CeSiumUA/homepost/main/ble_scanner.c

#include "ble_scanner.h"

static const char *TAG = __FILE__;

ble_scanned_device_cb_t ble_scanned_device_cb;

static esp_ble_scan_params_t ble_scan_params = {
    .scan_type              = BLE_SCAN_TYPE_PASSIVE,
    .own_addr_type          = BLE_ADDR_TYPE_PUBLIC,
    .scan_filter_policy     = BLE_SCAN_FILTER_ALLOW_ALL,
    .scan_interval          = 0x50,
    .scan_window            = 0x30,
    .scan_duplicate         = BLE_SCAN_DUPLICATE_DISABLE
};

#ifdef CONFIG_HOMEPOST_PRINT_BLE_DEVICE_NAME
static void ble_scanner_get_device_name(esp_ble_gap_cb_param_t *param, char *name, int name_len){
    uint8_t *adv_name = NULL;
    uint8_t adv_name_len = 0;

    adv_name = esp_ble_resolve_adv_data(param->scan_rst.ble_adv, ESP_BLE_AD_TYPE_NAME_CMPL, &adv_name_len);

    if (adv_name != NULL && adv_name_len > 0) {
        snprintf(name, name_len, "%.*s", adv_name_len, adv_name);
    }
    else {
        snprintf(name, name_len, "Unknown device");
    }
}
#endif

static void ble_scanner_gap_cb(esp_gap_ble_cb_event_t event, esp_ble_gap_cb_param_t *param){
#ifdef CONFIG_HOMEPOST_PRINT_BLE_DEVICE_NAME
    char name[64];
#endif
    esp_err_t err;

    switch (event) {
        case ESP_GAP_BLE_SCAN_PARAM_SET_COMPLETE_EVT:
            ESP_LOGI(TAG, "ESP_GAP_BLE_SCAN_PARAM_SET_COMPLETE_EVT");
            if (param->scan_param_cmpl.status == ESP_BT_STATUS_SUCCESS) {
                ESP_LOGI(TAG, "Scan parameters set successfully");
                esp_ble_gap_start_scanning(0);
            }
            else {
                ESP_LOGE(TAG, "Unable to set scan parameters");
            }
            break;
        case ESP_GAP_BLE_SCAN_START_COMPLETE_EVT:
            if ((err = param->scan_start_cmpl.status) != ESP_BT_STATUS_SUCCESS) {
                ESP_LOGE(TAG, "Scan start failed: %s", esp_err_to_name(err));
            }
            break;
        case ESP_GAP_BLE_ADV_START_COMPLETE_EVT:
            if ((err = param->adv_start_cmpl.status) != ESP_BT_STATUS_SUCCESS) {
                ESP_LOGE(TAG, "Adv start failed: %s", esp_err_to_name(err));
            }
            break;
        case ESP_GAP_BLE_SCAN_RESULT_EVT:
            if (param->scan_rst.search_evt == ESP_GAP_SEARCH_INQ_RES_EVT){
#ifdef CONFIG_HOMEPOST_PRINT_BLE_DEVICE_NAME
                memset(name, 0, sizeof(name));
                ble_scanner_get_device_name(param, name, sizeof(name));
                ESP_LOGI(TAG, "Device found: %s, RSSI: %d dB", name, param->scan_rst.rssi);
#endif
                if (ble_scanned_device_cb != NULL){
                    ble_scanned_device_cb(param);
                }
            }
            break;
        case ESP_GAP_BLE_SCAN_STOP_COMPLETE_EVT:
            if ((err = param->scan_stop_cmpl.status) != ESP_BT_STATUS_SUCCESS){
                ESP_LOGE(TAG, "Scan stop failed: %s", esp_err_to_name(err));
            }
            else {
                ESP_LOGI(TAG, "Stop scan successfully");
            }
            break;
        case ESP_GAP_BLE_ADV_STOP_COMPLETE_EVT:
            if ((err = param->adv_stop_cmpl.status) != ESP_BT_STATUS_SUCCESS){
                ESP_LOGE(TAG, "Adv stop failed: %s", esp_err_to_name(err));
            }
            else {
                ESP_LOGI(TAG, "Stop adv successfully");
            }
            break;
        default:
            break;
    }
}

esp_err_t ble_scanner_init(void){
    esp_err_t ret;

    ESP_LOGI(TAG, "Initializing a BLE scanner...");

    ESP_ERROR_CHECK(esp_bt_controller_mem_release(ESP_BT_MODE_CLASSIC_BT));

    esp_bt_controller_config_t bt_cfg = BT_CONTROLLER_INIT_CONFIG_DEFAULT();
    ret = esp_bt_controller_init(&bt_cfg);
    if (ret != ESP_OK) {
        ESP_LOGE(TAG, "esp_bt_controller_init failed: %s", esp_err_to_name(ret));
        return ret;
    }

    ret = esp_bt_controller_enable(ESP_BT_MODE_BLE);
    if (ret != ESP_OK) {
        ESP_LOGE(TAG, "esp_bt_controller_enable failed: %s", esp_err_to_name(ret));
        return ret;
    }

    ret = esp_bluedroid_init();
    if (ret != ESP_OK) {
        ESP_LOGE(TAG, "esp_bluedroid_init failed: %s", esp_err_to_name(ret));
        return ret;
    }

    ret = esp_bluedroid_enable();
    if (ret != ESP_OK) {
        ESP_LOGE(TAG, "esp_bluedroid_enable failed: %s", esp_err_to_name(ret));
        return ret;
    }

    ESP_LOGI(TAG, "BLE scanner initialized");

    return ESP_OK;
}

esp_err_t ble_scanner_start(ble_scanned_device_cb_t cb){
    esp_err_t ret;

    ble_scanned_device_cb = cb;

    ESP_LOGI(TAG, "Starting a BLE scanner...");

    ret = esp_ble_gap_register_callback(ble_scanner_gap_cb);
    if (ret != ESP_OK) {
        ESP_LOGE(TAG, "esp_ble_gap_register_callback failed: %s", esp_err_to_name(ret));
        return ret;
    }

    ret = esp_ble_gap_set_scan_params(&ble_scan_params);
    if (ret == ESP_OK) {
        ESP_LOGI(TAG, "Scan parameters set successfully");
    }
    else {
        ESP_LOGE(TAG, "Unable to set scan parameters");
    }

    return ret;
}

esp_err_t ble_scanner_stop(void){
    esp_err_t ret;

    ESP_LOGI(TAG, "Stopping the BLE scanner...");

    ret = esp_ble_gap_stop_scanning();
    if (ret != ESP_OK) {
        ESP_LOGE(TAG, "esp_ble_gap_stop_scanning failed: %s", esp_err_to_name(ret));
        return ret;
    }

    return ESP_OK;
}

esp_err_t ble_scanner_deinit(void){
    ESP_LOGI(TAG, "Deinitializing the BLE scanner...");

    esp_bluedroid_disable();
    esp_bluedroid_deinit();
    esp_bt_controller_disable();
    esp_bt_controller_deinit();

    ESP_ERROR_CHECK(esp_bt_controller_mem_release(ESP_BT_MODE_BLE));

    return ESP_OK;
}
